RK3AZB-MIET/PPP/Models/Гетеродин.cir

[Main]
FileType=CIR
Version=11.01
Program=Micro-Cap
Component Version=10.00
Shape Version=11.00
Screen=1920,1080
MCAPVersion=11.0.1.9
Key ID=0
NLCnt=48
TXCnt=4

[shapedef]
Name=Battery
Line=0,0,22,0
Line=22,-3,22,3
Line=26,-7,26,7
Line=26,0,48,0
Current=32,8,16,8

[shapedef]
Name=Bjt.root
Line=0,0,13,0
Rectangle=13,-12,15,12
Current=32,-24,32,-16
Current=32,24,32,16
Current=0,-8,8,-8
PolyOpen=3
PolyLine=24,-24
PolyLine=24,-12
PolyLine=14,-2
PolyOpen=3
PolyLine=24,24
PolyLine=24,12
PolyLine=14,2

[shapedef]
Name=Capacitor
Line=0,0,22,0
Line=22,-8,22,8
Line=26,-8,26,8
Line=26,0,48,0
Current=32,12,16,12
Ellipse=29,-7,31,-5
FColor=#0000FF

[shapedef]
Name=Diode
Root="Diode.root",0,0,0

[shapedef]
Name=Diode.root
Line=0,0,20,0
Line=28,0,48,0
Rectangle=18,-8,20,8
PolyClosed=3
PolyLine=20,0
PolyLine=28,-8
PolyLine=28,8
Current=32,16,16,16

[shapedef]
Name=Ground
Line=0,0,12,0
Line=12,-8,12,8
Line=18,-4,18,4
Line=24,0,24,0

[shapedef]
Name=Inductor
Line=42,0,48,0
Line=0,0,5,0
Arc=5,-7,17,7 , 11,-7,5,0
Arc=13,-7,25,7 , 19,-7,13,0
Arc=29,-7,41,7 , 35,-7,29,0
Arc=21,-7,33,7 , 27,-7,21,0
Arc=6,-7,18,7 , 18,0,12,-7
Arc=14,-7,26,7 , 26,0,20,-7
Arc=22,-7,34,7 , 34,0,28,-7
Arc=30,-7,42,7 , 42,0,36,-7
Line=11,-7,12,-7
Line=19,-7,20,-7
Line=27,-7,28,-7
Line=35,-7,36,-7
Arc=13,-4,17,2 , 13,-1,15,2
Arc=29,-4,33,2 , 29,-1,31,2
Arc=21,-4,25,2 , 21,-1,23,2
Arc=14,-4,18,2 , 16,2,18,-1
Arc=30,-4,34,2 , 32,2,34,-1
Arc=22,-4,26,2 , 24,2,26,-1
Line=15,2,16,2
Line=23,2,24,2
Line=31,2,32,2
Line=5,5,9,5
Line=41,5,41,9
Line=39,7,43,7
Current=32,8,16,8

[shapedef]
Name=PNP
Root="Bjt.root",0,0,0
PolyClosed=3
PolyLine=17,-5
PolyLine=21,-5
PolyLine=17,-9
Line=16,-4,14,-2
Line=16,4,14,2

[shapedef]
Name=Resistor_Euro
Rectangle=12,-4,36,4
FColor=None
Line=0,0,12,0
Line=48,0,36,0
Current=32,8,16,8
Ellipse=31,-1,33,1
FColor=#0000FF

[compdef]
Name=Capacitor
Definition=Capacitor
Shape=Capacitor
Mask=6913
Used=1108
memo=Capacitor
Label Offset=4,-38,12,12
PinCnt=2
Pin="Plus",6,0,-3,-5
Pin="Minus",0,0,-14,-5

[compdef]
Name=Resistor
Definition=Resistor
Shape=Resistor_Euro
Mask=6913
Used=2046
memo=Resistor
Label Offset=11,-36,10,10
PinCnt=2
Pin="Plus",6,0,-10,-4
Pin="Minus",0,0,-14,-4

[compdef]
Name=Ground
Definition=Ground
Shape=Ground
Mask=1793
Used=951
memo=Ground
Label Offset=0,0,0,0
PinCnt=1
Pin="PinA",0,0,-3,-7

[compdef]
Name=Inductor
Definition=Inductor
Shape=Inductor
Mask=6401
Used=100
memo=Inductor
Label Offset=18,9,11,12
PinCnt=2
Pin="Plus",6,0,-5,-9
Pin="Minus",0,0,-3,-9

[compdef]
Name=Battery
Definition=Battery
Shape=Battery
Mask=4865
Used=71
memo=Battery
Label Offset=19,7,10,13
PinCnt=2
Pin="Plus",6,0,-4,-5
Pin="Minus",0,0,-10,-5

[compdef]
Name=BC557C
Definition=PNP
Shape=PNP
Mask=4992
Used=5
memo=PNP Amplifier Transistor Vceo=-45V Ic=-.1A Pd=625mW
Label Offset=29,-11,-3,25
PinCnt=3
Pin="Collector",3,3,6,5
Pin="Base",0,0,-19,-3
Pin="Emitter",3,-3,6,8
Power=0.625

[compdef]
Name=1N4007
Definition=Diode
Shape=Diode
Mask=6016
Used=23
memo=General Purpose Rectifier Vr=1000V Io=1A
Label Offset=18,10,12,12
PinCnt=2
Pin="Anode",6,0,-13,-8
Pin="Cathode",0,0,-27,-8

[Circuit]
Window Placement=2,3, -1,-1, -8,-31, 78,78,1004,670
Default Object=Color=#000080
Default Object Font=Height=-15,FStyle=0,Color=#000080,Name=Arial
Default Object Apply Border To Text=No
Default Object Apply Fill To Text=No
NodeVoltageFormat=3
PathDelayFormat=3
WarningFormat=3
GridTextFormulaFormat=3
Window Placement in Transient Analysis=2,3, -1,-1, -8,-31, 78,78,1004,670
SpiceType=AMBIGUOUS
Title_Block_Border=None
Title_Block=False
Show Nodes=False
Show Voltages=True
Show Current=False
Show Power=False
Show Condition=False
Show Pin Connections=False
Show Connection Warnings=False
Show Cross=False
Show Attribute Text=True
Show Grid Text=True

[Comp]
Name=Capacitor
Px=712,464
Rot=1

[Attr]
ON=12,12,PART
V=C1
Style=8192

[Attr]
ON=12,26,CAPACITANCE
V=0.047u
Style=8192

[Attr]
ON=0,0,PACKAGE
V

[Comp]
Name=Resistor
Px=664,464
Rot=1

[Attr]
ON=10,10,PART
V=R1
Style=8192

[Attr]
ON=10,24,RESISTANCE
V=100k
Style=8192

[Attr]
ON=0,0,PACKAGE
V

[Comp]
Name=Ground
Px=688,536
Rot=7

[Wire]
Pxs=664,464,688,464

[Wire]
Pxs=688,448,688,464

[Wire]
Pxs=688,464,712,464

[Wire]
Pxs=664,512,688,512

[Wire]
Pxs=688,512,688,536

[Wire]
Pxs=688,512,712,512

[Comp]
Name=Resistor
Px=848,424
Rot=2

[Attr]
ON=-27,22,PART
V=R2
Style=8192

[Attr]
ON=-26,8,RESISTANCE
V=2k
Style=8192

[Attr]
ON=0,0,PACKAGE
V

[Comp]
Name=Capacitor
Px=784,440
Rot=1

[Attr]
ON=12,12,PART
V=C2
Style=8192

[Attr]
ON=12,26,CAPACITANCE
V=4700p
Style=8192

[Attr]
ON=0,0,PACKAGE
V

[Comp]
Name=Ground
Px=784,488
Rot=7

[Comp]
Name=Capacitor
Px=712,368
Rot=2

[Attr]
ON=-21,24,PART
V=C3
Style=8192

[Attr]
ON=-36,10,CAPACITANCE
V=180p
Style=8192

[Attr]
ON=0,0,PACKAGE
V

[Wire]
Pxs=712,424,720,424

[Wire]
Pxs=784,424,784,440

[Wire]
Pxs=784,424,800,424

[Wire]
Pxs=712,368,720,368

[Wire]
Pxs=720,368,720,424

[Wire]
Pxs=720,424,784,424

[Comp]
Name=Capacitor
Px=616,472
Rot=3

[Attr]
ON=-29,-26,PART
V=C4
Style=8192

[Attr]
ON=-33,-45,CAPACITANCE
V=100
Style=8192

[Attr]
ON=0,0,PACKAGE
V

[Comp]
Name=Ground
Px=616,520
Rot=7

[Comp]
Name=Resistor
Px=552,480
Rot=1

[Attr]
ON=10,10,PART
V=R3
Style=8192

[Attr]
ON=10,24,RESISTANCE
V=100k
Style=8192

[Attr]
ON=0,0,PACKAGE
V

[Wire]
Pxs=552,472,552,480

[Wire]
Pxs=552,472,616,472

[Comp]
Name=Ground
Px=552,576
Rot=7

[Comp]
Name=Capacitor
Px=552,528
Rot=1

[Attr]
ON=12,12,PART
V=C5
Style=8192

[Attr]
ON=12,26,CAPACITANCE
V=10u
Style=8192

[Attr]
ON=0,0,PACKAGE
V

[Wire]
Pxs=616,424,664,424

[Wire]
Pxs=664,368,664,424

[Comp]
Name=Inductor
Px=512,424
Rot=1

[Attr]
ON=11,12,PART
V=L1
Style=8192

[Attr]
ON=11,26,INDUCTANCE
V=5u
Style=8192

[Attr]
ON=0,0,PACKAGE
V

[Comp]
Name=Ground
Px=512,472
Rot=7

[Wire]
Pxs=512,424,616,424

[Comp]
Name=Battery
Px=920,480
Rot=3

[Attr]
ON=-26,-27,PART
V=V1
Style=8192

[Attr]
ON=-18,-41,VALUE
V=6

[Attr]
ON=0,0,PACKAGE
V

[Comp]
Name=Ground
Px=920,480
Rot=7

[Comp]
Name=BC557C
Px=688,448
Rot=5

[Attr]
ON=-1,-39,PART
V=Q1
Style=8192

[Attr]
ON=47,-53,MODEL
V=BC557C

[Attr]
ON=33,-67,POWER
V=0.625

[Attr]
ON=35,-95,PACKAGE
V=TO-92

[Comp]
Name=Resistor
Px=448,472
Rot=3

[Attr]
ON=-26,-24,PART
V=R4
Style=8192

[Attr]
ON=-25,-38,RESISTANCE
V=3.3k
Style=8192

[Attr]
ON=0,0,PACKAGE
V

[Comp]
Name=Resistor
Px=448,632
Rot=3

[Attr]
ON=-26,-24,PART
V=R5
Style=8192

[Attr]
ON=-25,-38,RESISTANCE
V=1k
Style=8192

[Attr]
ON=0,0,PACKAGE
V

[Comp]
Name=Ground
Px=448,632
Rot=7

[Comp]
Name=Resistor
Px=448,472
Rot=1

[Attr]
ON=10,10,PART
V=R6
Style=8192

[Attr]
ON=10,25,RESISTANCE
V=a
Style=8192

[Attr]
ON=0,0,PACKAGE
V

[Comp]
Name=Resistor
Px=448,536
Rot=1

[Attr]
ON=10,10,PART
V=R7
Style=8192

[Attr]
ON=10,24,RESISTANCE
V=10k-a
Style=8192

[Attr]
ON=0,0,PACKAGE
V

[Wire]
Pxs=448,520,448,528

[Wire]
Pxs=448,528,552,528

[Wire]
Pxs=552,528,552,536

[Wire]
Pxs=448,528,448,536

[Comp]
Name=1N4007
Px=616,472
Rot=7

[Attr]
ON=-29,12,PART
V=D4
Style=8192

[Attr]
ON=-61,26,MODEL
V=1N4007

[Attr]
ON=-52,54,PACKAGE
V=DO-41

[Comp]
Name=Capacitor
Px=712,320
Rot=2

[Attr]
ON=-21,24,PART
V=C6
Style=8192

[Attr]
ON=-36,10,CAPACITANCE
V=150p
Style=8192

[Attr]
ON=0,0,PACKAGE
V

[Wire]
Pxs=712,320,720,320

[Wire]
Pxs=720,320,720,368

[Wire]
Pxs=664,320,664,368

[Grid Text]
Text=".define a 0"
Px=352,528
GridSnap=True
JustifyH=Left
JustifyV=Bottom
CBorder=None

[Grid Text]
Text="Vcc"
Px=920,432
GridSnap=True
JustifyH=Left
JustifyV=Bottom
CBorder=None

[Grid Text]
Text="Vcc"
Px=848,424
GridSnap=True
JustifyH=Left
JustifyV=Bottom
CBorder=None

[Grid Text]
Text="Vcc"
Px=448,424
GridSnap=True
JustifyH=Left
JustifyV=Bottom
CBorder=None

[Schematic]
CurrentSection 0=0
CurrentSection 1=0
CurrentSection 2=0
CurrentSection 3=0
Splitter.xs=0
Splitter.ys=0
TextQuad=4099
Scale=0.5
GridUser=10
ShapeGroups="Main","Euro","Polarity","Main1","Main2","Electrolytic","GroundArrow","DeMorgan"
CalcRMS=False
CalcAVG=False
CalcPeak=False
CalcVoltage=True
DisplayMeasure=Last
ShareScales=True

[Tools]
Pos=Top
FILESAVEASOLD=No
BOM=No
FILEPCB=No
PROBE=Yes
SELECT=Yes
COMP=Yes
TEXT=Yes
WIRE=Yes
WIRED=Yes
BUS=Yes
GRAPHIC=Yes
LINE=No
ELLIPSE=No
RECT=No
DIAM=No
ARC=No
PIE=No
LEFTBRK=No
RIGHTBRK=No
BOTHBRK=No
META=Yes
FLAG=Yes
INFO=Yes
HELP=Yes
HELP_SPICE=No
LINK=Yes
REGION_ENABLE=Yes
TITLE_BLOCK=Yes
DIGTRC=No
DIGTRC2=No
BUILD_COMMAND=Yes
DIGALL=No
GRIDTEXT=Yes
COMPTEXT=Yes
NODE=Yes
MEASURED=Yes
NODEV=Yes
CURRENT=Yes
POWER=Yes
CONDITIN=Yes
PIN=Yes
CONNWARN=Yes
CROSS=Yes
GRID=Yes
BORDER=Yes
BORDERONE=Yes
TITLE=Yes
RUBBER=Yes
PROPERTY=Yes
STEP=Yes
MIRROR=Yes
ROTATE=Yes
FLIPY=Yes
FLIPX=Yes
CIR_MAKEMACRO=No
CLEARCUTWIRE=No
CLIPBOARDCIRPAGE2BMM=No
FINDCOMP=Yes
FIND=Yes
REPEAT=No
REPLACE=No
MODEL=Yes
CIR2CKT=Yes
ATTDISP=Yes
ENABLE=Yes
DISABLE=Yes
TOFRONT=Yes
TOBACK=Yes
SELNEXT=Yes
PAGEADD=Yes
PAGEADDTEXT=No
ADDSECTION=No
PAGEDEL=Yes
ZOOMIN=Yes
ZOOMOUT=Yes
AUTOSCALECIR=Yes
GOTOFLAG=Yes
UPLEVEL=Yes
COLOR=Yes
FONT=Yes
DM_LAST=No
DM_RMS=No
DM_AVG=No
DM_PEAK=No
GRID_NONE=No
GRID_NORMAL=No
GRID_BOLD_5=No
GRID_BOLD_6=No
GRID_BOLD_USER=No
GRAPH_PAPER=No
SPLITCIRTEXTH=No
SPLITCIRTEXTV=No
SPACE_SPLITTERS_EVENLY=No
NORMALCIR=No
RENAMEDEFINE=No
RENAMECMP=No
ATTALIGN=No
RESETNODEPOS=No
FIT2STANDARD=No
NODESNAP=No
MOVETEXT=No
TEXTINC=No
TOGGLETEXT=No
TOGGLEMODE=No
TOLERANCE=No
ALIGNLEFT=Yes
ALIGNRIGHT=Yes
ALIGNTOP=Yes
ALIGNBOTTOM=Yes

[Section]
Index=0
Name="Гетеродин"
Type=Main
Enable=True
CurrentPage 0=0
CurrentPage 1=0
CurrentPage 2=0
CurrentPage 3=0
TabSize 0=425
TabSize 1=425
TabSize 2=425
TabSize 3=425

[Page]
Index=0
Section=0
Print=True
Enable=True
Name=Main
PrinterScale=1
Scale 0=1
Scale 1=1
Scale 2=1
SB 3=344,312
Scale 3=0.5
Px=743,620
WinBackGround Color=#FFFFFF
Select Color=#FF0000
Anchor Color=#000000
Select Box Color=#000080
Grid Text Color=Height=-12,FStyle=0,Color=#0000FF,Name=Verdana
Grid Text RTF=False
Grid Text Angle=0
Grid Text GridSnap=True
Grid Text PinIt=False
Grid Text JustifyH=Left
Grid Text JustifyV=Bottom
Component Color=#0000FF
Attribute Text=Height=-12,FStyle=0,Color=#008000,Name=Verdana
Wire Color=#008000
Bus Color=#008000
Pin Connection=Height=-10,FStyle=0,Color=#FF0000,Name=Arial
Pin Marker Color=#008000
Node Number=Height=-11,FStyle=0,Color=#FF00FF,Name=Arial
Node Voltage Color=Height=-11,FStyle=0,Color=#000000,Name=Arial
Dynamic AC Voltage Color=#E4E4E4
Text Banner Text=Height=-15,FStyle=0,Color=#800000,Name=Arial
Title Block Background=#C0C0C0
Current=Height=-11,FStyle=0,Color=#0000FF,Name=Arial
Power/Condition=Height=-11,FStyle=0,Color=#FF0000,Name=Arial
Digital Path Color=#FF0000
Title Block Border=#000000
Disabled	Color=#C0C0C0
Search Color=#FFFF00
Grid Color=#000000
Graph Paper=#E4E4E4
Digital 0 Color=#000000
Digital R Color=#FFFF00
Digital F Color=#FFFF00
Digital 1 Color=#FF0000
Digital X Color=#C0C0C0
Digital Z Color=#808080
Block Select Color=#51F998

[Page]
Index=1
Section=0
Type=Text
Print=False
Enable=True
Name=Text
Font=Height=-15,FStyle=0,Color=#000000,Name=Courier New
Comment Color=#008000
WinBackGround Color=#FFFFFF
Disabled	Color=#C0C0C0
KeyWord Color=#0000FF
Error	Color=#FF0000
Search Color=#FFFF00

[Page]
Index=2
Section=0
Type=Text
Print=False
Enable=True
Name=Models
SB 0=19,1
Font=Height=-15,FStyle=0,Color=#000000,Name=Courier New
Comment Color=#008000
WinBackGround Color=#FFFFFF
Disabled	Color=#C0C0C0
KeyWord Color=#0000FF
Error	Color=#FF0000
Search Color=#FFFF00

[Page]
Index=3
Section=0
Type=Info
Print=False
Enable=True
Name=Info
Font=Height=-15,FStyle=0,Color=#000000,Name=Courier New
Comment Color=#008000
WinBackGround Color=#FFFFFF
Disabled	Color=#C0C0C0
KeyWord Color=#0000FF
Error	Color=#FF0000
Search Color=#FFFF00

[Text Area]
Section=0
Page=1

[Text Area]
Section=0
Page=2
Text=
Text=.MODEL BC557 NPN ()

[InfoPage]
InfoPage=True
Warnings=True
System=True
Defines=True
Array=True
Model=True
Measure=True
MacroSubckt=True
NotUsed=True
ComponentCounts=True

[Transient]
WinID=1
Window Placement=2,3, -1,-1, -8,-31, 78,78,1004,670
Font=Height=-19,FStyle=0,Color=#0000FF,Name=Arial
WinBackGround Color=#FFFFFF
Select Color=#FF0000
Anchor Color=#000000
Select Box Color=#000080
Title
AutoTitle=Yes
Grid Color=#808080
Grid Weight=1
Grid Pattern=Dot6
Tracker Foreground=Height=-15,FStyle=0,Color=#000000,Name=Arial
Tracker Background=#FFFF00
Baseline color=#0000FF
BaseLine Weight=1
CurveFit color=#FF0000
CurveFit Weight=2
CurveFit Pattern=Dash
Static Grids=False
PlusMark=False
MinorLog25=Off
LabelMinor=Off
DataPoints=False
Token=False
Ruler=False
XAxisGrids=True
YAxisGrids=True
MinorLogGrids=True
BaseLine=False
AlignZ=True
Align Cursors=True
TagFormatX=3
TagFormatY=3
FormulaFormat=2
EndMode=SCALE
Graph Background=#FFFFFF
Tracker Intercept=False
Tracker Mouse=True
Tracker Cursor=True
Tracker Cursor BranchInfo=False
Horizontal Cursor=False
Same Y Scales=Yes
Enable X Scaling=True
Enable Y Scaling=True
Keep X Scales The Same=True
Number of Grids X=5
Number of Grids Y=5
Cursor Select Color Primary=#C0C0C0
Cursor Select Color Secondary=#FF0000
Data Point Labels Color Fore=Height=-15,FStyle=0,Color=#000000,Name=Arial
Data Point Labels Color Back=#FFFF00
OperPoint=True
OperPointOnly=False
AutoScaleRanges=False
FixedTimeStep=False
DoPSS=False
PSS_Periods="1"
PSS_Iterations="5"
PSS_Error="1u"
PSS_ShowPlots=True
FFT_NPts="8192"
FFT_IncludeDCHarmonic=False
FFT_AutoScale_Harmonics="10"
PrinterAutoTile=No
PrinterBlackBorder=No
MonMaxShow=2
MonPageWidth=66
MonPlotWidth=21
MonExprXWidth=142
MonExprYWidth=306
MonRangeXWidth=90
MonRangeYWidth=90
AnimateWait=None
AnimateWaitTime=500
AnimatePressAfter=0
Save_For_Future=No
Reduce_Display=1
Reduce_Save=1
Reduce_ThrowDataOut=0
Num Out Header Left
Num Out Header Center="$MC\n$user\n$company\n$Analysis of $name\n$date $time"
Num Out Header Right
Num Out Delimiter=32
Num Out Write=True
Num Out Write Main Header=True
Num Out Write Limits=True
Num Out Write Branch Header=True
Num Out Write Models=False
Num Out Write Zero Models=True
Num Out Write Undefined Models=True
Num Out Write Operating Point=True
Num Out Write Measurement Values=True
Num Out Write Values=True
Num Out Write Waveform Header=True
Num Out Allow Dup Y Expr=False
Num Out Low="TSTART"
Num Out High="TMAX"
Num Out Font=Height=-15,FStyle=0,Color=#000000,Name=Courier New
Num Out Format=3
Num Out HideNonSelected=False
AutoSaveWave=False
Wave Format=16E
State Variables Format=5E
Print Individual Pages=False

[Tools]
Pos=Top
SELECT=Yes
GRAPHIC=Yes
LINE=No
ELLIPSE=No
RECT=No
DIAM=No
ARC=No
PIE=No
LEFTBRK=No
RIGHTBRK=No
BOTHBRK=No
META=Yes
POLYCLOS=No
SCALE=Yes
CURSOR=Yes
MEASUREH=Yes
MEASUREV=Yes
TAG=Yes
PTAG=Yes
TEXT=Yes
PROPERTY=Yes
START=Yes
STOP=Yes
PAUSE=Yes
RESUME=No
DATAPTS=Yes
TOKENS=Yes
RULER=Yes
PLUS=Yes
XAXIS=Yes
YAXIS=Yes
MINORLOG=Yes
LOG25=Yes
BASELINE=Yes
HORIZCUR=Yes
GOTOX=Yes
GOTOY=Yes
GOTOPERF=Yes
GOTOBRNC=Yes
CLEAR_ACCUMULATED=Yes
PDELETE_ALL_PLOTS=Yes
NEXT=Yes
NEXTIN=Yes
PEAK=Yes
VALLEY=Yes
HIGH=Yes
LOW=Yes
INFLECTN=Yes
GHIGH=Yes
GLOW=Yes
BOTTOM=Yes
TOP=Yes
WAVEFORMBUFFER=Yes
AOUTPUT=Yes
PKEY=Yes
ENXSCALE=Yes
ENYSCALE=Yes
ZOOMIN=Yes
ZOOMOUT=Yes
AUTOSCALE=Yes
RESTORESCALE=No
COLOR=Yes
FONT=Yes
SELNEXT=Yes
NORMALIZE=No
NORMALIZE_MIN=No
NORMALIZE_MAX=No
ADD_TAG_LEFT=No
ADD_TAG_RIGHT=No
ADD_HORZ_TAG=No
ADD_VERT_TAG=No
ALIGN_CURSORS=No
ALIGN_CURSORSZ=No
CURSORTOCLIPBOARD=No
TRACKER_CURSOR=No
TRACKER_CURSOR_BRANCHINFO=No
TRACKER_INTERCEPT=No
TRACKER_MOUSE=No
TOFRONT=Yes
TOBACK=Yes
SPLITCIRTEXTH=No
SPLITCIRTEXTV=No
SPACE_SPLITTERS_EVENLY=No
NORMALCIR=No
LABEL_WAVEFORM=No
LABEL_DATA_POINTS=No
WFB_ADD_TO_LIMITS=No
ENVELOPE=No
SAMEYSCALES=No
KEEPXSCALESTHESAME=No
CURVEFIT=No
SHOWWATCH=No
BP=No
TOGGLEMODE=No
REMOVEALLTEXT=No
AUTOSCALEX=No
LABELALLMINOR=No
ALIGNLEFT=Yes
ALIGNRIGHT=Yes
ALIGNTOP=Yes
ALIGNBOTTOM=Yes

[APage]
Analysis=Transient
Name="Main"

[AObject]
Analysis=Transient
Object=PTag
EndPoint=ArrowF
CBorder=#000080
w=0
AliasID1=1
Pos=3.1586376208404606e-006,-0.069129387818167257,3.4446108501732561e-006,-0.069129387818167257
Posm=-0.091411603597958385
Font=Height=-15,FStyle=0,Color=#000080,Name=Arial
Format=3
FormatY=3
Text="Frequency(V(L1),1,10)"

[Monte Carlo Options]
Analysis=Transient
Status=Off
Zero Tolerance=False
Eliminate Outliers=False
Distribution=Normal
Number of Runs=10
Seed=0

[Limits]
Analysis=Transient
TRange=10u
TStep=0.01u
NPts=250
Temp=27
RetraceRuns=1
StateVar=Zero
RunOption=Normal
Temperature Type=Linear
Accumulate Plots=False
IgnoreExprErrors=False

[WaveForm]
Analysis=Transient
Plt=1
AliasID=1
XExp=T
YExp=V(L1)
XRng=AutoAlways
YRng=AutoAlways
Options=LINEARX,LINEARY
Enable=Enable
Line Color=#0000FF
Text Color=#0000FF
Rainbow=False
VFmtX=3
VFmtY=3
ScaleFactorX="None"
ScaleFactorY="None"
ScaleUnitsX="Auto"
ScaleUnitsY="Auto"
SFmtX=2
SFmtY=2
NOFmtX=3E
NOFmtY=3E

[WaveForm]
Analysis=Transient
AliasID=-1
Options=LINEARX,LINEARY
Enable=Enable
Line Color=#008000
Text Color=#008000
Rainbow=False
VFmtX=3
VFmtY=3
ScaleFactorX="None"
ScaleFactorY="None"
ScaleUnitsX="Auto"
ScaleUnitsY="Auto"
SFmtX=2
SFmtY=2
NOFmtX=3E
NOFmtY=3E

[Limits]
Analysis=DynamicAC
Temp=27
FreqList=1E6
SliderPer=10
FirstValueDisplay=Mag
SecondValueDisplay=PhaseDeg
PlaceText=True
TextPx=303,362

[Limits]
Analysis=DynamicDC
Temp=27
SliderPer=10
PlaceText=True

[Pane]
Analysis=Transient
CurrentPage 0="Main"

[Pane]
Analysis=AC

[Pane]
Analysis=DC

[Pane]
Analysis=HmDistortion

[Pane]
Analysis=ImDistortion

[Pane]
Analysis=Stability

[Watch]
Analysis=Transient
Format=3
ExprPercentWidth=80

[WCTolerance]
Var Width=100
Nominal Width=72
Tol Width=152

[Slider]
Analysis=Transient
Link="PARAM a"
Min="0"
Max="10K"
Default="5K"
Format=3
Method=Linear
Show=True
Font=Height=-15,FStyle=0,Color=#000000,Name=Arial
StepSize="10%"
MRUDockID=59421
Floating=False
LocalOffset=True
Rect=-2,45,75,205

[Slider]
Analysis=DynamicDC
Link="PARAM a"
Min="0"
Max="10k"
Default="100"
Format=3
Method=Linear
Show=True
Font=Height=-15,FStyle=0,Color=#000000,Name=Arial
StepSize="10%"
MRUDockID=59421
Floating=False
LocalOffset=True
Rect=-2,45,75,205

[OPMethods]
Analysis=Transient
Standard Newton-Raphson=0,0
Source Stepping=0,0
Diagonal Gmin Stepping=0,0
Junction Gmin Stepping=0,0
Pseudo Transient=0,0

[OPMethods]
Analysis=AC
Standard Newton-Raphson=0,0
Source Stepping=0,0
Diagonal Gmin Stepping=0,0
Junction Gmin Stepping=0,0
Pseudo Transient=0,0

[OPMethods]
Analysis=DC
Standard Newton-Raphson=0,0
Source Stepping=0,0
Diagonal Gmin Stepping=0,0
Junction Gmin Stepping=0,0
Pseudo Transient=0,0

[OPMethods]
Analysis=HmDistortion
Standard Newton-Raphson=0,0
Source Stepping=0,0
Diagonal Gmin Stepping=0,0
Junction Gmin Stepping=0,0
Pseudo Transient=0,0

[OPMethods]
Analysis=ImDistortion
Standard Newton-Raphson=0,0
Source Stepping=0,0
Diagonal Gmin Stepping=0,0
Junction Gmin Stepping=0,0
Pseudo Transient=0,0

[OPMethods]
Analysis=Stability
Standard Newton-Raphson=0,0
Source Stepping=0,0
Diagonal Gmin Stepping=0,0
Junction Gmin Stepping=0,0
Pseudo Transient=0,0

[OPMethods]
Analysis=DynamicAC
Standard Newton-Raphson=0,0
Source Stepping=0,0
Diagonal Gmin Stepping=0,0
Junction Gmin Stepping=0,0
Pseudo Transient=0,0

[OPMethods]
Analysis=DynamicDC
Standard Newton-Raphson=0,0
Source Stepping=0,0
Diagonal Gmin Stepping=0,0
Junction Gmin Stepping=0,0
Pseudo Transient=0,0
